petaflot/saunactrl/data/wood_horizontal_bar.jpg

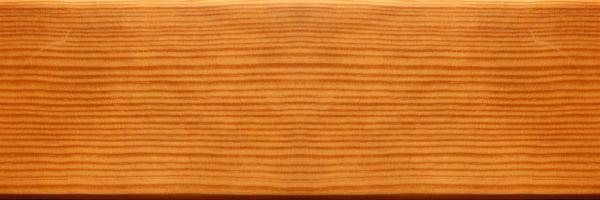
data/wood_horizontal_bar.jpg
