petaflot/saunactrl/data/wood_simple.jpg

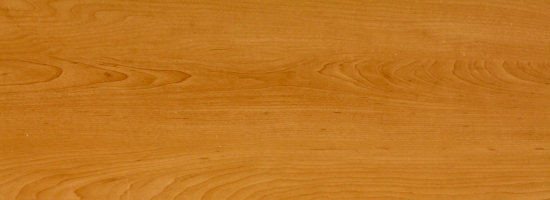
data/wood_simple.jpg
