petaflot/saunactrl/data/wood_vertical_wall.jpg

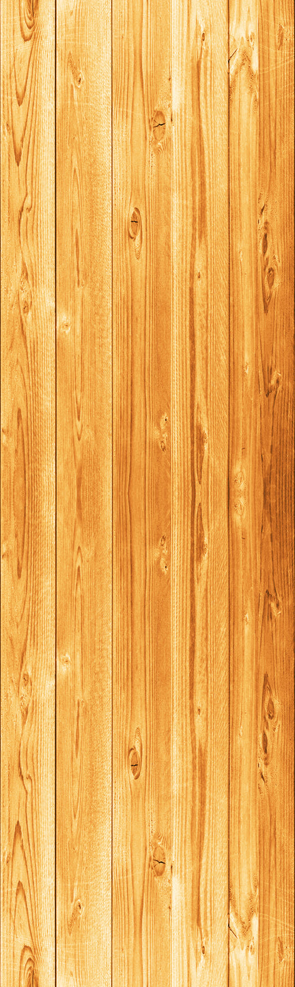
data/wood_vertical_wall.jpg
